hf7y/crt/provision/dexter/zaxon/compose.yaml

# zaxon on dexter, at /srv/zaxon/. Deploy and the one-owner rule: see README.
services:
  gateway:
    # PULLED, NOT BUILT: a dexter that lost its checkout recovers from this file.
    image: ghcr.io/hf7y/zaxon:latest
    container_name: zaxon-gateway
    restart: always
    volumes:
      # ORIGINAL absolute paths, both: the venv's shebangs and its python symlink
      # (to the uv-managed 3.11) are absolute and dangle at any other mount point.
      - ./data:/home/zaxon/.hermes
      - ./uv:/home/zaxon/.local/share/uv
    # BOUND, NOT AUTHENTICATED: this distro also carries 192.168.0.22, so
    # "8643:8643" gave the house LAN ask_zach (#402). Naming addresses IS the guard.
    ports:
      - "127.0.0.1:8643:8643"
      - "100.107.253.56:8643:8643"
    environment:
      # NOT in data/.env, which .deploykeep shields from every deploy -- which is
      # why the repo's whisper_stt.sh never ran. But .env is loaded with
      # override=True and BEATS this, so the old line stays commented out there.
      HERMES_LOCAL_STT_COMMAND: /opt/zaxon-relay/bin/whisper_stt.sh {input_path} {output_dir} {language}

  # THE MCP DOOR, separate as it was in the distro: it owns ask_zach.
  relay:
    image: ghcr.io/hf7y/zaxon:latest
    container_name: zaxon-relay
    restart: always
    volumes:
      - ./data/zaxon_relay:/home/zaxon/.hermes/zaxon_relay
      - ./data/cache:/home/zaxon/.hermes/cache
      - ./data/logs:/home/zaxon/.hermes/logs
      - ./data/hermes-agent:/home/zaxon/.hermes/hermes-agent:ro
      - ./data/.env:/home/zaxon/.hermes/.env:ro
      - ./data/config.yaml:/home/zaxon/.hermes/config.yaml:ro
      - ./data/channel_directory.json:/home/zaxon/.hermes/channel_directory.json:ro
      - ./uv:/home/zaxon/.local/share/uv
    environment:
      # crt#194: unset = the door stays unauthenticated (today's behavior, and
      # what a fresh `docker compose up` gets with no secret configured). To
      # require it, put ZAXON_SHARED_SECRET=... in a `.env` file next to this
      # compose.yaml (gitignored, NOT data/.env -- the relay process itself
      # never reads that mount, only the gateway's hermes_cli bootstrap does)
      # and send the same value as the X-Zaxon-Shared-Secret header.
      ZAXON_SHARED_SECRET: ${ZAXON_SHARED_SECRET:-}
    working_dir: /opt/zaxon-relay
    # `hermes send` reaches the Baileys bridge on localhost:3000, a gateway child.
    # The bridge listens on 127.0.0.1 only and refuses a non-loopback Host header
    # (hermes-agent's bridge.js), so this cannot move to a network of its own.
    network_mode: "service:gateway"
    # The IMAGE's python: hermes-agent's venv leads PATH and has no `mcp`.
    command: ["/usr/local/bin/python", "/opt/zaxon-relay/zaxon_relay_server.py"]
    depends_on:
      - gateway
    healthcheck:
      # crt#322: probing OUR OWN 8643 always passes even stranded in the
      # gateway's old namespace after a restart -- we're the one listening
      # on it. The bridge at 3000 lives in the gateway container itself, so
      # only it tells a live namespace from an orphaned one. A failing
      # healthcheck is visibility only (Docker doesn't restart on it); the
      # actual recovery is zaxon_relay_netns_guard's self-exit.
      test: ["CMD", "/usr/local/bin/python", "-c", "import socket,sys; s=socket.create_connection(('127.0.0.1',3000),5); s.close()"]
      interval: 60s
      timeout: 10s
      retries: 3
      start_period: 30s

  # Tails agent.log for Zach's replies, matching them to tickets. Reads only.
  watcher:
    image: ghcr.io/hf7y/zaxon:latest
    container_name: zaxon-watcher
    restart: always
    volumes:
      - ./data/zaxon_relay:/home/zaxon/.hermes/zaxon_relay
      - ./data/cache:/home/zaxon/.hermes/cache
      - ./data/logs:/home/zaxon/.hermes/logs
      - ./data/hermes-agent:/home/zaxon/.hermes/hermes-agent:ro
      - ./data/.env:/home/zaxon/.hermes/.env:ro
      - ./data/config.yaml:/home/zaxon/.hermes/config.yaml:ro
      - ./data/channel_directory.json:/home/zaxon/.hermes/channel_directory.json:ro
      - ./uv:/home/zaxon/.local/share/uv
    working_dir: /opt/zaxon-relay
    network_mode: "service:gateway"
    command: ["/usr/local/bin/python", "/opt/zaxon-relay/zaxon_relay_watcher.py"]
    depends_on:
      - relay
    healthcheck:  # crt#322: same stale-namespace signal as relay's, above
      test: ["CMD", "/usr/local/bin/python", "-c", "import socket,sys; s=socket.create_connection(('127.0.0.1',3000),5); s.close()"]
      interval: 60s
      timeout: 10s
      retries: 3
      start_period: 30s
